petrkucerak/SPD1/gateway/gateway-schema/gateway-schema.kicad_sch

## KiCad design gateway/gateway-schema/gateway-schema.kicad_sch (2024-05-20)

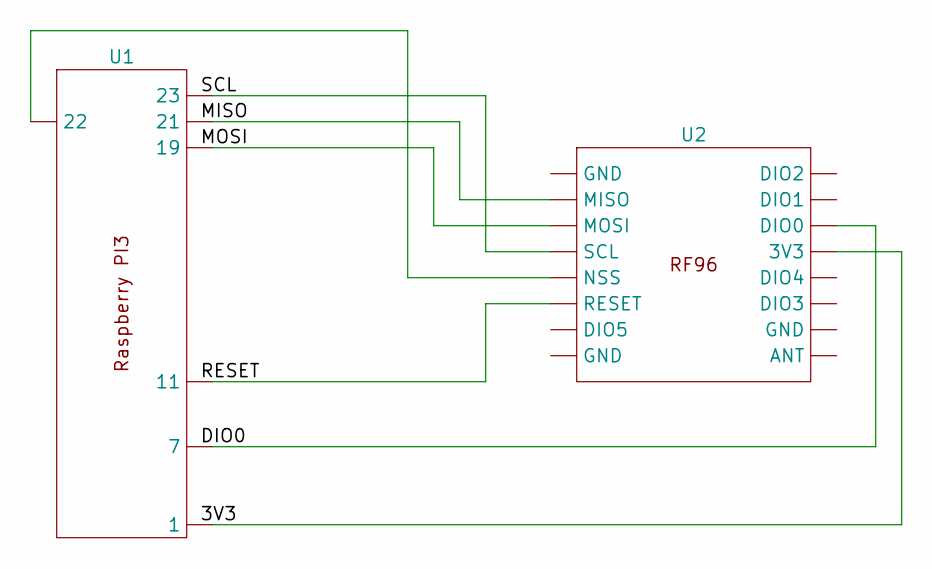
[picture p4: schematic gateway-schema.kicad_sch]

Parts:
U1, U2: (no value)

Connections:
unnamed: U1., U2.
